shaneraible/bopit/software/bp_src/keypad_test/keypad_test.ino

// Use this example with the Adafruit Keypad products.
// You'll need to know the Product ID for your keypad.
// Here's a summary:
//   * PID3844 4x4 Matrix Keypad
//   * PID3845 3x4 Matrix Keypad
//   * PID1824 3x4 Phone-style Matrix Keypad
//   * PID1332 Membrane 1x4 Keypad
//   * PID419  Membrane 3x4 Matrix Keypad

#include "Adafruit_Keypad.h"

// define your specific keypad here via PID
#define KEYPAD_PID3845
// define your pins here
// can ignore ones that don't apply
#define R1    A3
#define R2    7
#define R3    6
#define R4    4
#define C1    A4
#define C2    A2
#define C3    5
// leave this import after the above configuration
#include "keypad_config.h"

//initialize an instance of class NewKeypad
Adafruit_Keypad customKeypad = Adafruit_Keypad( makeKeymap(keys), rowPins, colPins, ROWS, COLS);

void setup() {
  Serial.begin(9600);
  customKeypad.begin();
}

void loop() {
  // put your main code here, to run repeatedly:
  customKeypad.tick();

  while(customKeypad.available()){
    keypadEvent e = customKeypad.read();
    Serial.print((char)e.bit.KEY);
    if(e.bit.EVENT == KEY_JUST_PRESSED) Serial.println(" pressed");
    else if(e.bit.EVENT == KEY_JUST_RELEASED) Serial.println(" released");
  }

  delay(10);
}
